Jin-Neuron/Turtle-Pico/board/advanced/pic/PCB_3D/3D-Bottom.png

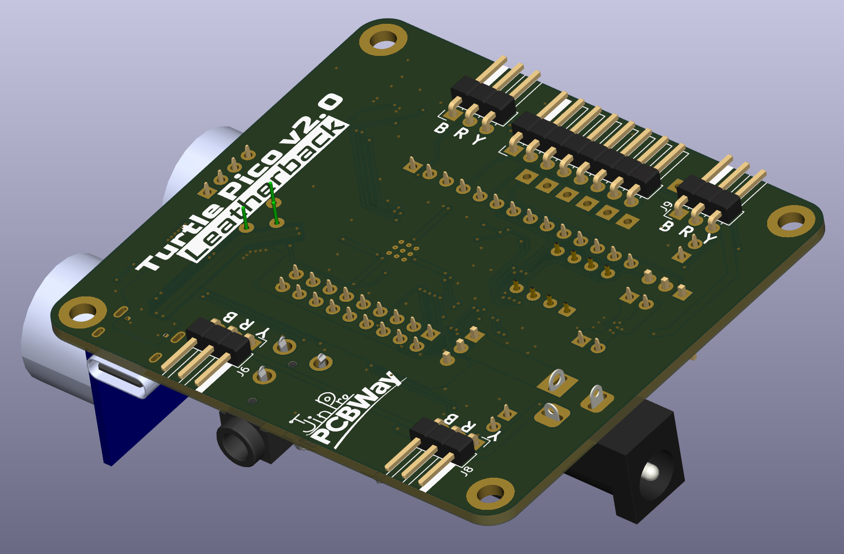
board/advanced/pic/PCB_3D/3D-Bottom.png
