Jin-Neuron/Turtle-Pico/board/advanced/pic/PCB_3D/3D-Top.png

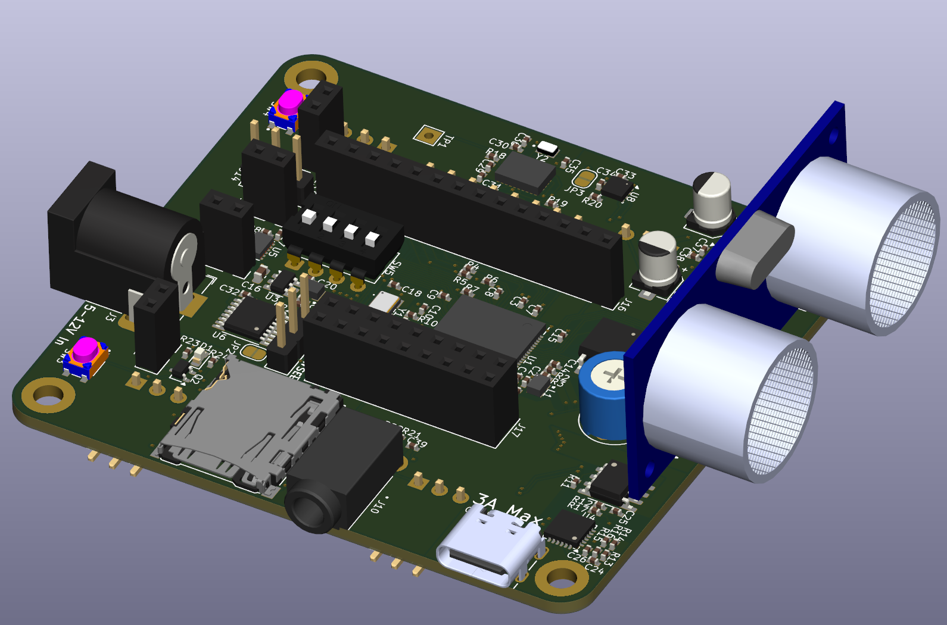
board/advanced/pic/PCB_3D/3D-Top.png
