Jin-Neuron/Turtle-Pico/board/advanced/pic/PCB_3D/BottomPCB.png

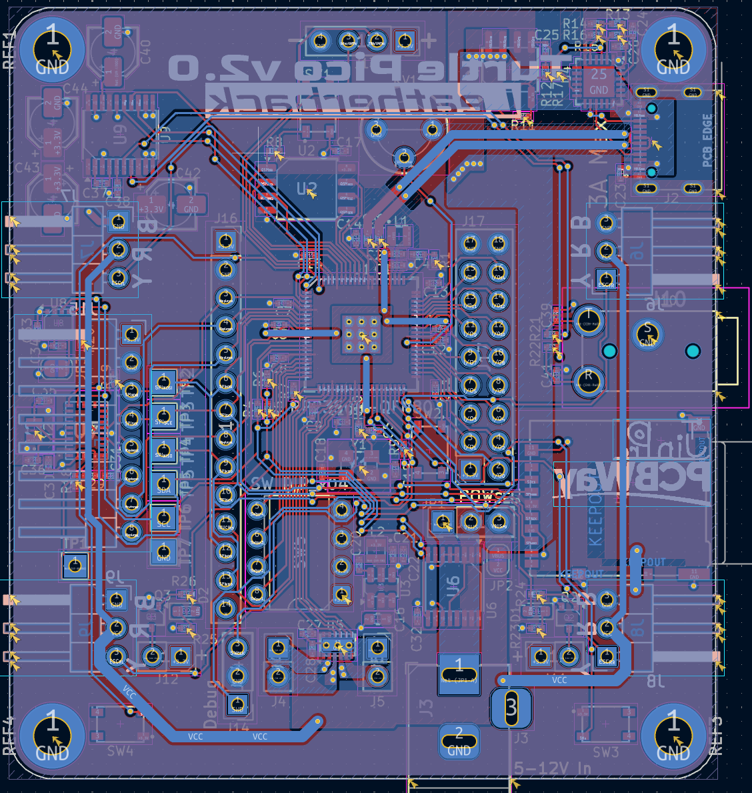
board/advanced/pic/PCB_3D/BottomPCB.png
