Jin-Neuron/Turtle-Pico/board/advanced/pic/PCB_3D/FrontPCB.png

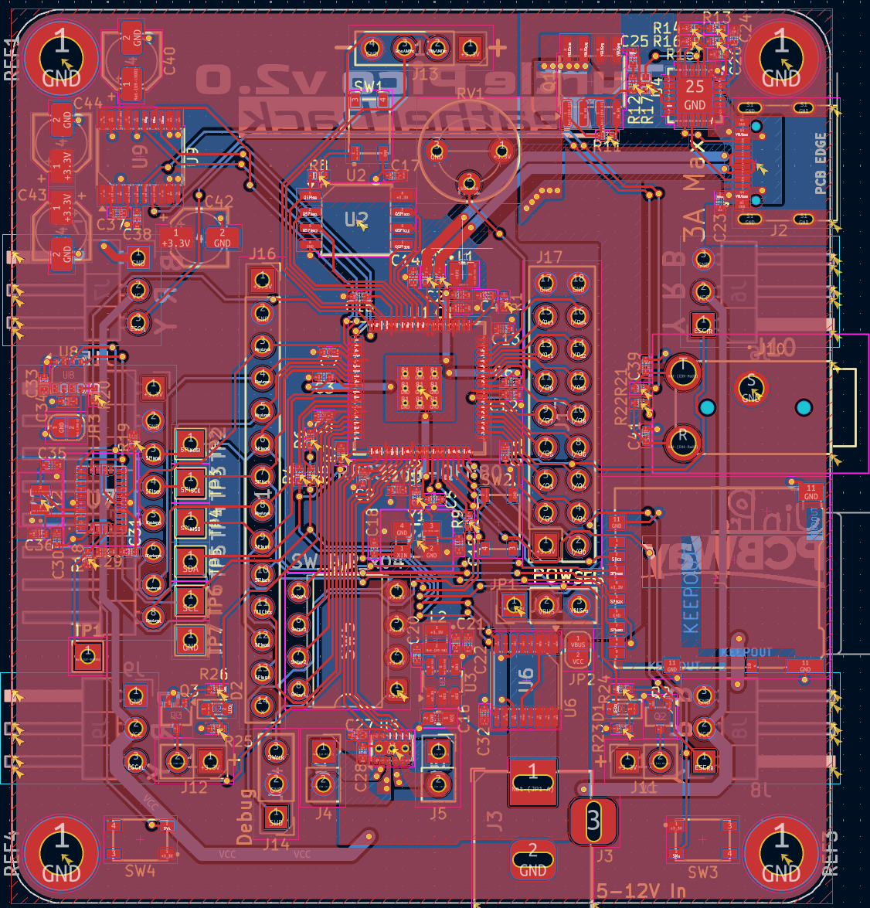
board/advanced/pic/PCB_3D/FrontPCB.png
