Jin-Neuron/Turtle-Pico/board/advanced/pic/schematics/MotorPart.png

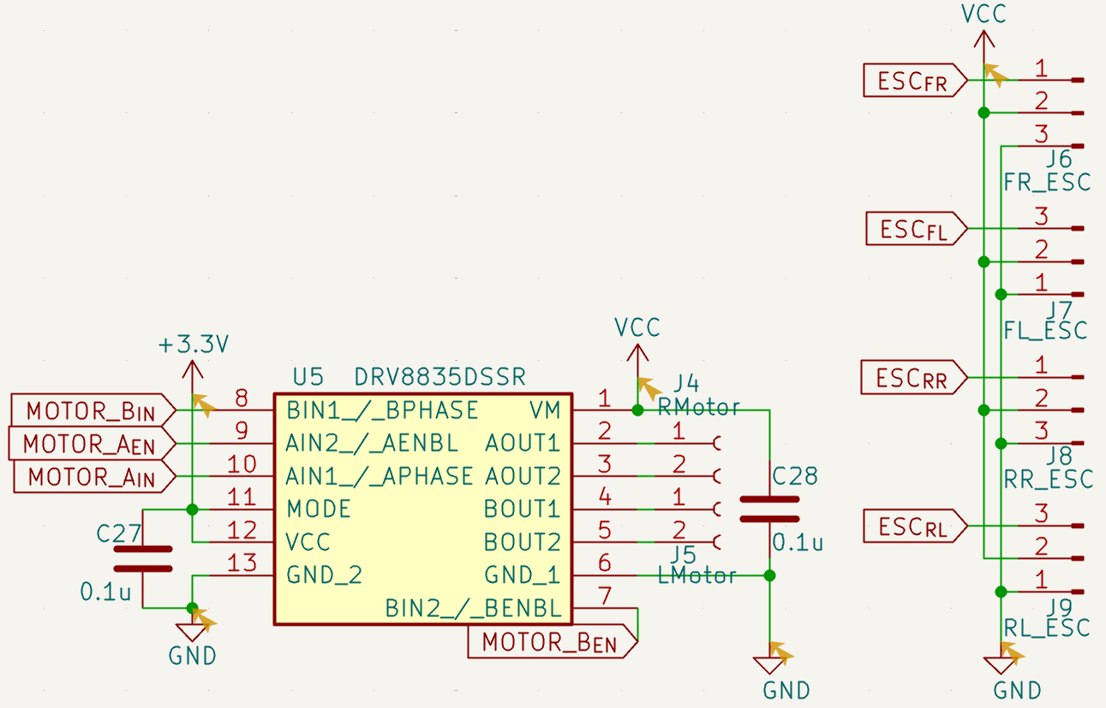
board/advanced/pic/schematics/MotorPart.png
