Jin-Neuron/Turtle-Pico/board/advanced/pic/schematics/StoragePart.png

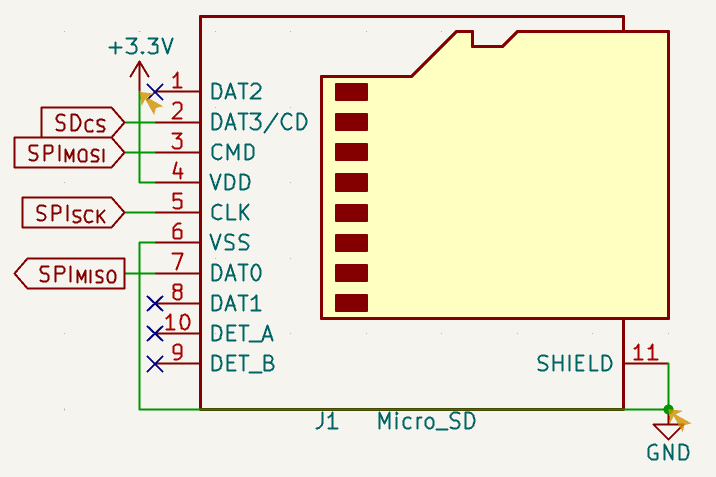
board/advanced/pic/schematics/StoragePart.png
