Jin-Neuron/Turtle-Pico/board/main/pic/Package_Close.png

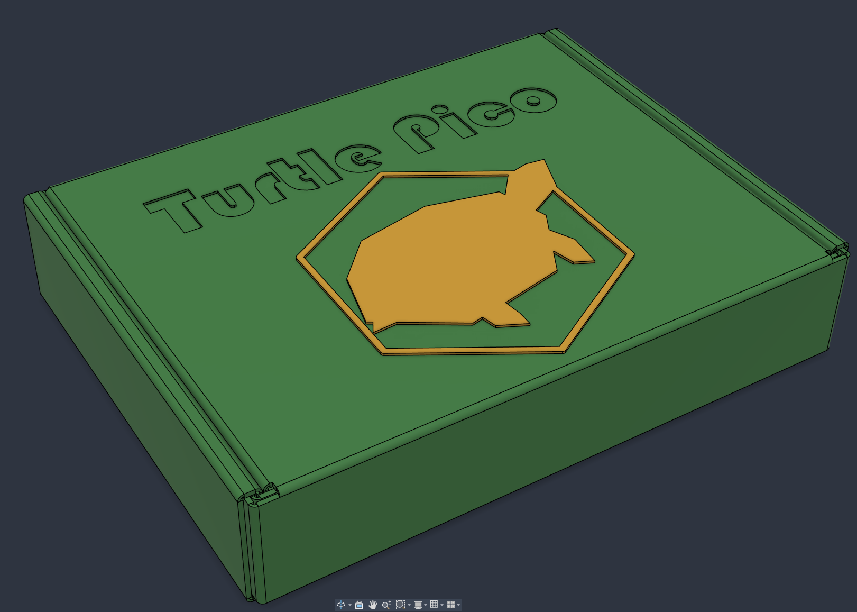
board/main/pic/Package_Close.png
