Jin-Neuron/Turtle-Pico/board/main/pic/Package_Open.png

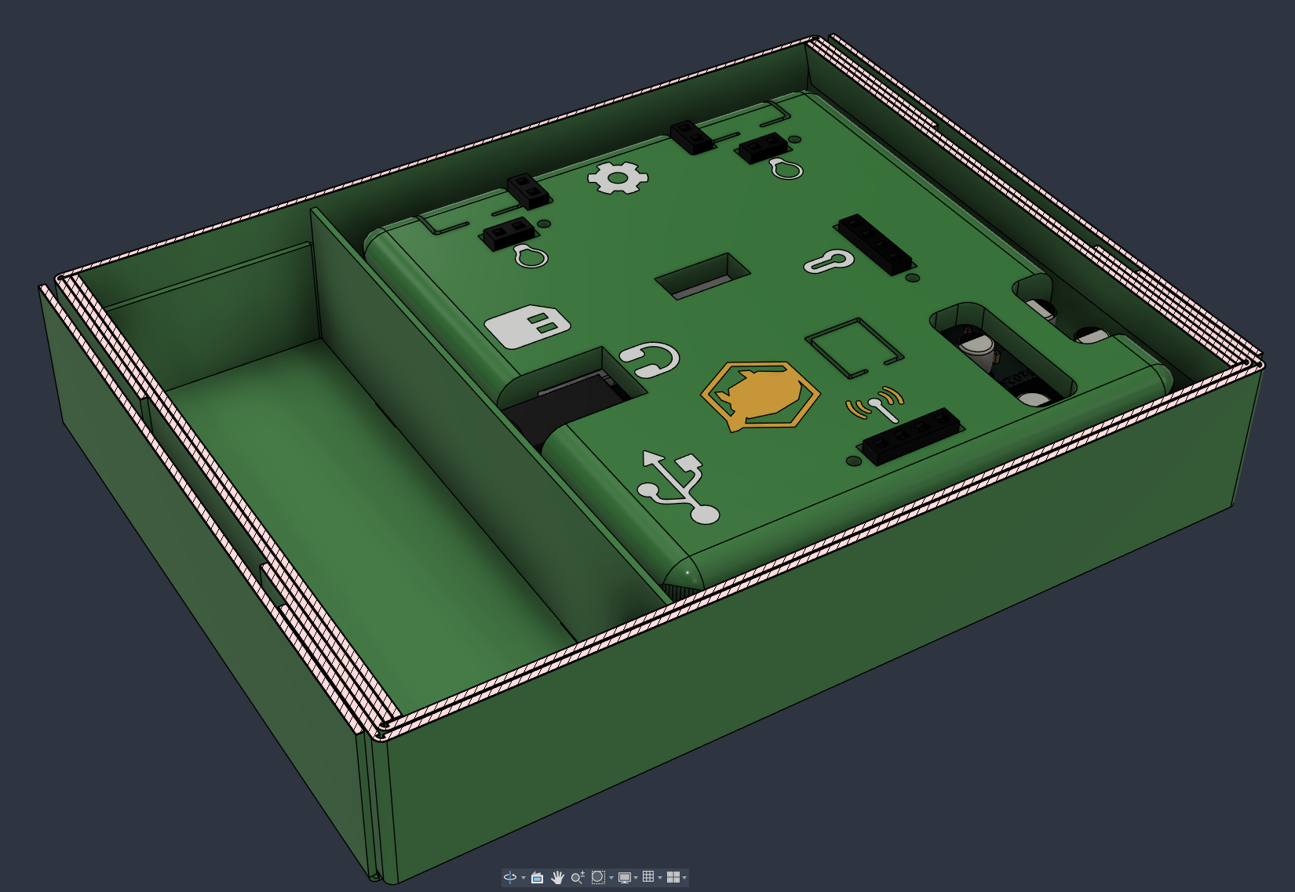
board/main/pic/Package_Open.png
