Jin-Neuron/Turtle-Pico/board/main/pic/TurtlePico_Case_1.png

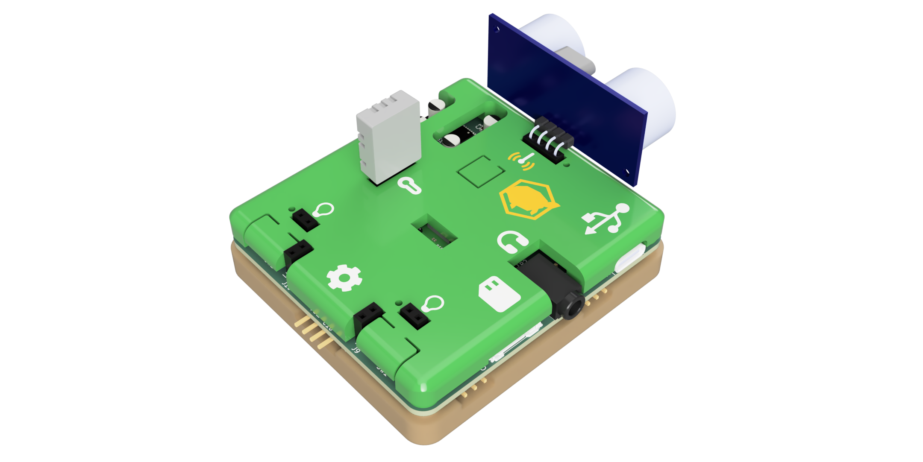
board/main/pic/TurtlePico_Case_1.png
