Jin-Neuron/Turtle-Pico/board/main/pic/TurtlePico_Case_2.png

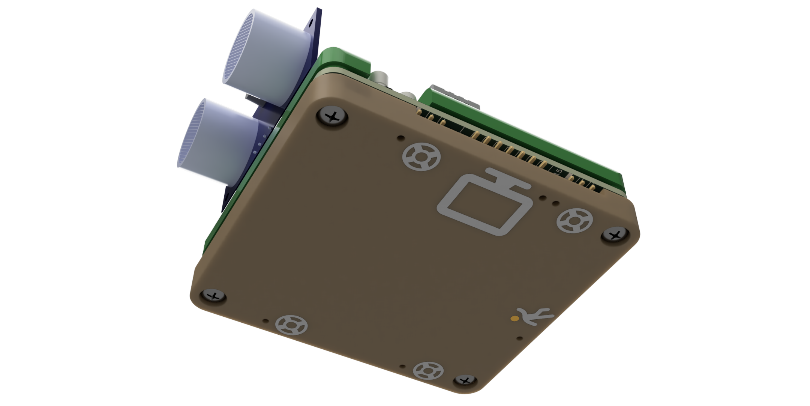
board/main/pic/TurtlePico_Case_2.png
