Jin-Neuron/Turtle-Pico/board/main/pic/v.2/3D_1.png

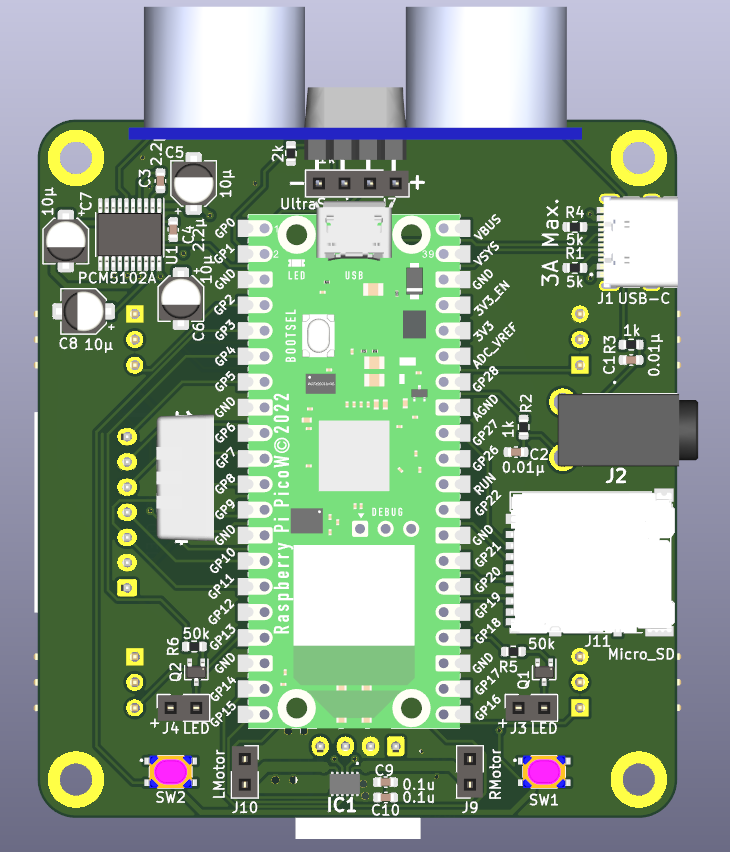
board/main/pic/v.2/3D_1.png
