Jin-Neuron/Turtle-Pico/board/main/pic/v.2/3D_3.png

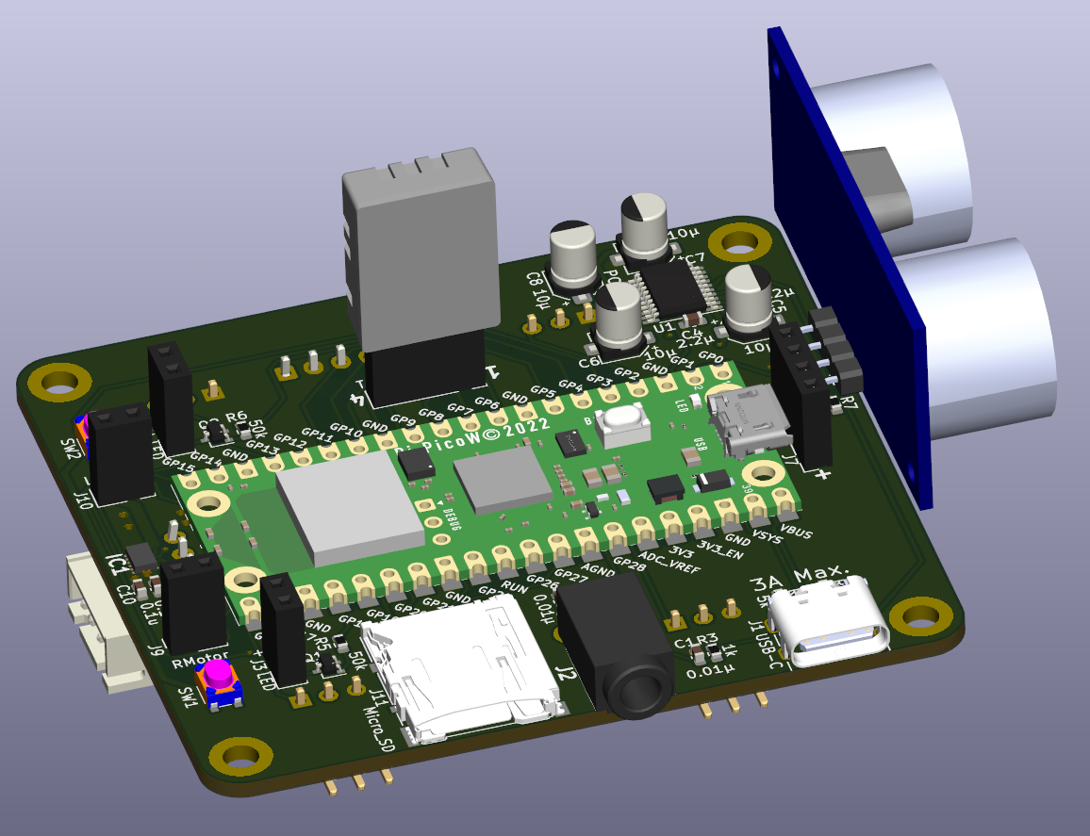
board/main/pic/v.2/3D_3.png
