Jin-Neuron/Turtle-Pico/board/main/pic/v.2/PCB_1.png

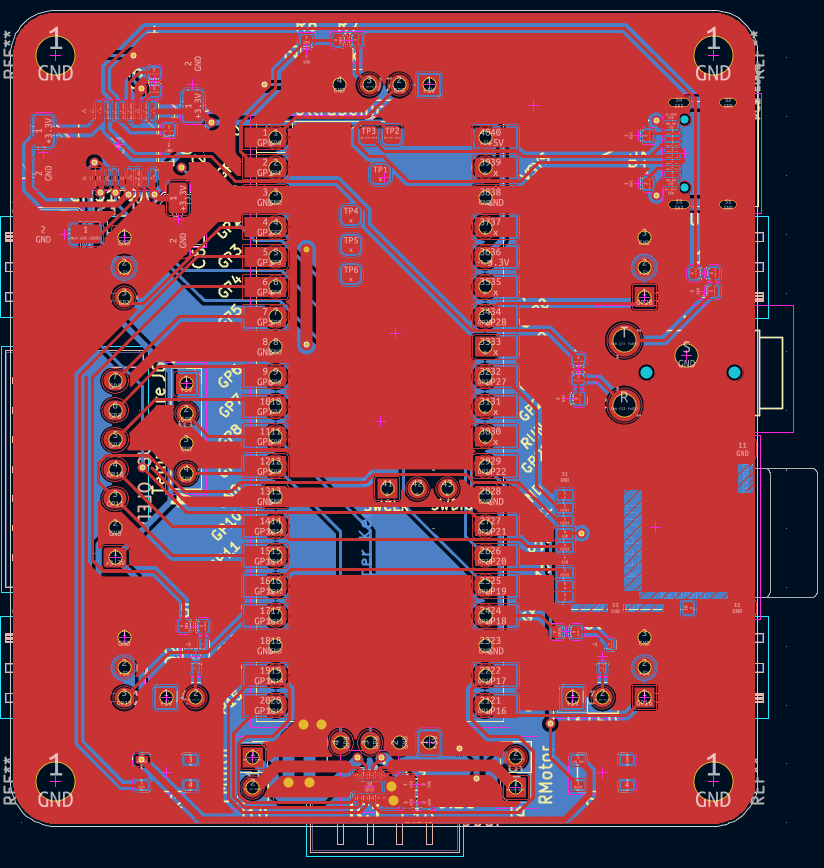
board/main/pic/v.2/PCB_1.png
