Jin-Neuron/Turtle-Pico/board/main/pic/v.2/PCB_2.png

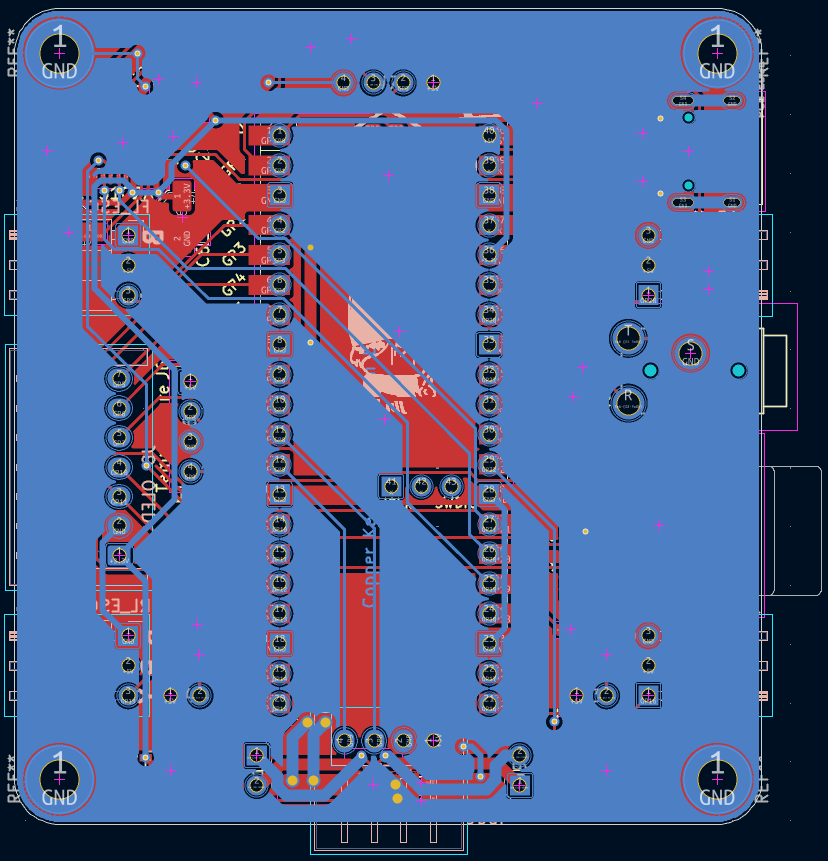
board/main/pic/v.2/PCB_2.png
