Jin-Neuron/Turtle-Pico/board/main/pic/v.2/shematics.png

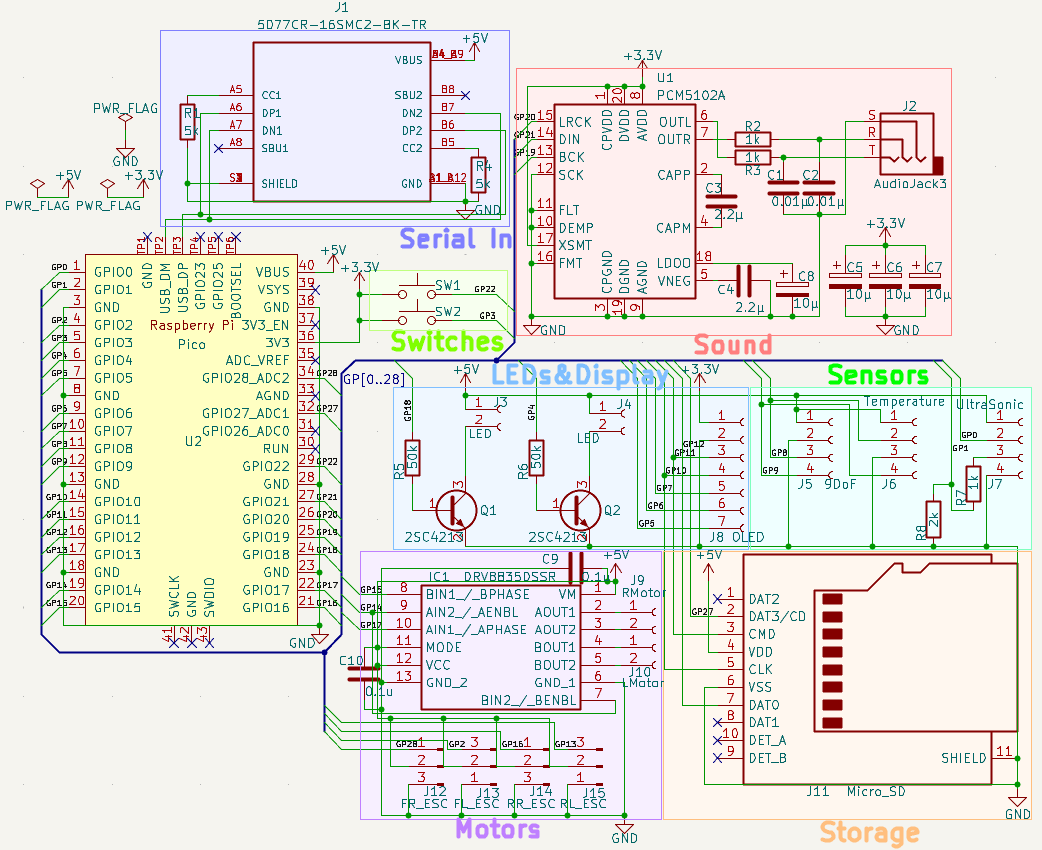
board/main/pic/v.2/shematics.png
