Jin-Neuron/Turtle-Pico/example/Car/img/JinNeuron.jpg

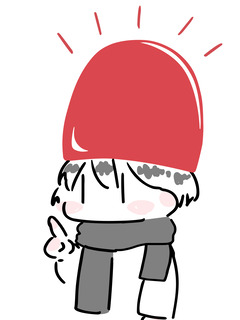
example/Car/img/JinNeuron.jpg
