Jin-Neuron/Turtle-Pico/example/Car/img/TUT_2.jpg

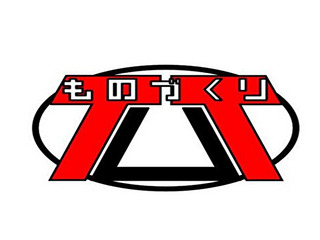
example/Car/img/TUT_2.jpg
