Jin-Neuron/Turtle-Pico/example/Turtle Dashboard/st7789/img/clock_back.png

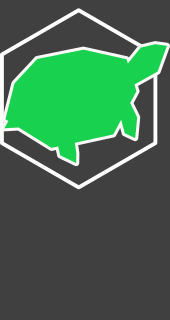
example/Turtle Dashboard/st7789/img/clock_back.png
