Jin-Neuron/Turtle-Pico/example/Turtle Dashboard/st7789/img/JinTurtle.png

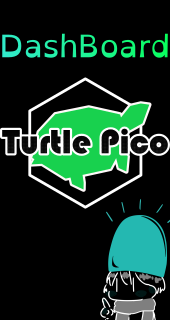
example/Turtle Dashboard/st7789/img/JinTurtle.png
