Jin-Neuron/Turtle-Pico/example/TestLeatherback/vga2_bold_16x32.py

WIDTH = 16
HEIGHT = 32
FIRST = 0
LAST = 255
_FONT = \nb'\x00\x00\x00\x00\x00\x00\x00\x00\x00\x00\x00\x00\x00\x00\x00\x00\x00\x00\x00\x00\x00\x00\x00\x00\x00\x00\x00\x00\x00\x00\x00\x00\x00\x00\x00\x00\x00\x00\x00\x00\x00\x00\x00\x00\x00\x00\x00\x00\x00\x00\x00\x00\x00\x00\x00\x00\x00\x00\x00\x00\x00\x00\x00\x00'\nb'\x00\x00\x00\x00\x00\x00\x00\x00\x3f\xfc\x3f\xfc\x60\x06\x60\x06\xc0\x03\xc0\x03\xcc\x33\xcc\x33\xc0\x03\xc0\x03\xc0\x03\xc0\x03\xcf\xf3\xcf\xf3\xc3\xc3\xc3\xc3\xc0\x03\xc0\x03\x60\x06\x60\x06\x3f\xfc\x3f\xfc\x00\x00\x00\x00\x00\x00\x00\x00\x00\x00\x00\x00'\nb'\x00\x00\x00\x00\x00\x00\x00\x00\x3f\xfc\x3f\xfc\x7f\xfe\x7f\xfe\xff\xff\xff\xff\xf3\xcf\xf3\xcf\xff\xff\xff\xff\xff\xff\xff\xff\xf0\x0f\xf0\x0f\xfc\x3f\xfc\x3f\xff\xff\xff\xff\x7f\xfe\x7f\xfe\x3f\xfc\x3f\xfc\x00\x00\x00\x00\x00\x00\x00\x00\x00\x00\x00\x00'\nb'\x00\x00\x00\x00\x00\x00\x00\x00\x00\x00\x00\x00\x1e\x78\x1e\x78\x3f\xfc\x3f\xfc\x7f\xfe\x7f\xfe\x7f\xfe\x7f\xfe\x7f\xfe\x7f\xfe\x3f\xfc\x3f\xfc\x1f\xf8\x1f\xf8\x07\xe0\x07\xe0\x01\x80\x01\x80\x00\x00\x00\x00\x00\x00\x00\x00\x00\x00\x00\x00\x00\x00\x00\x00'\nb'\x00\x00\x00\x00\x00\x00\x00\x00\x00\x00\x00\x00\x01\x80\x01\x80\x03\xc0\x03\xc0\x07\xe0\x07\xe0\x0f\xf0\x0f\xf0\x1f\xf8\x1f\xf8\x0f\xf0\x0f\xf0\x07\xe0\x07\xe0\x03\xc0\x03\xc0\x01\x80\x01\x80\x00\x00\x00\x00\x00\x00\x00\x00\x00\x00\x00\x00\x00\x00\x00\x00'\nb'\x00\x00\x00\x00\x00\x00\x00\x00\x03\xc0\x03\xc0\x07\xe0\x07\xe0\x07\xe0\x07\xe0\x3c\x3c\x3c\x3c\x7c\x3e\x7c\x3e\x7c\x3e\x7c\x3e\x3c\x3c\x3c\x3c\x03\xc0\x03\xc0\x03\xc0\x03\xc0\x03\xc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

FONT = memoryview(_FONT)
