Jin-Neuron/Turtle-Pico/example/TestLeatherback/bme280_test.py

import time
import st7789
import tft_config
from machine import Pin, PWM, I2C
from lib.bme280 import Bme_280

bme = Bme_280(1, Pin("I2C_SCL"), Pin("I2C_SDA"))

for i in range(5):
    print(bme.read_data())
    time.sleep(3)
